UzixLS/zx-tsid/images/revA-side2.jpg

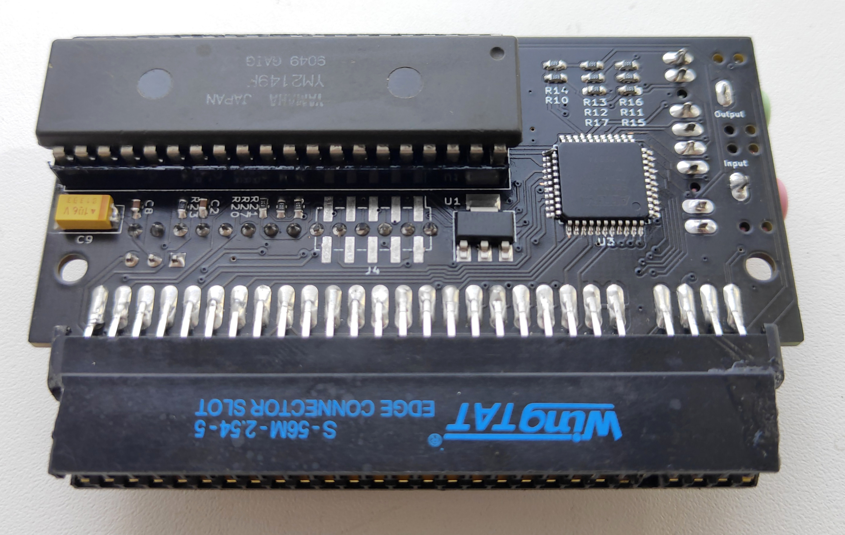
images/revA-side2.jpg
